derekzyl/smart-incubator/incubator_new_circuit/incubator_new_circuit.kicad_sch

## KiCad design incubator_new_circuit/incubator_new_circuit.kicad_sch (2026-01-31, an earlier design)

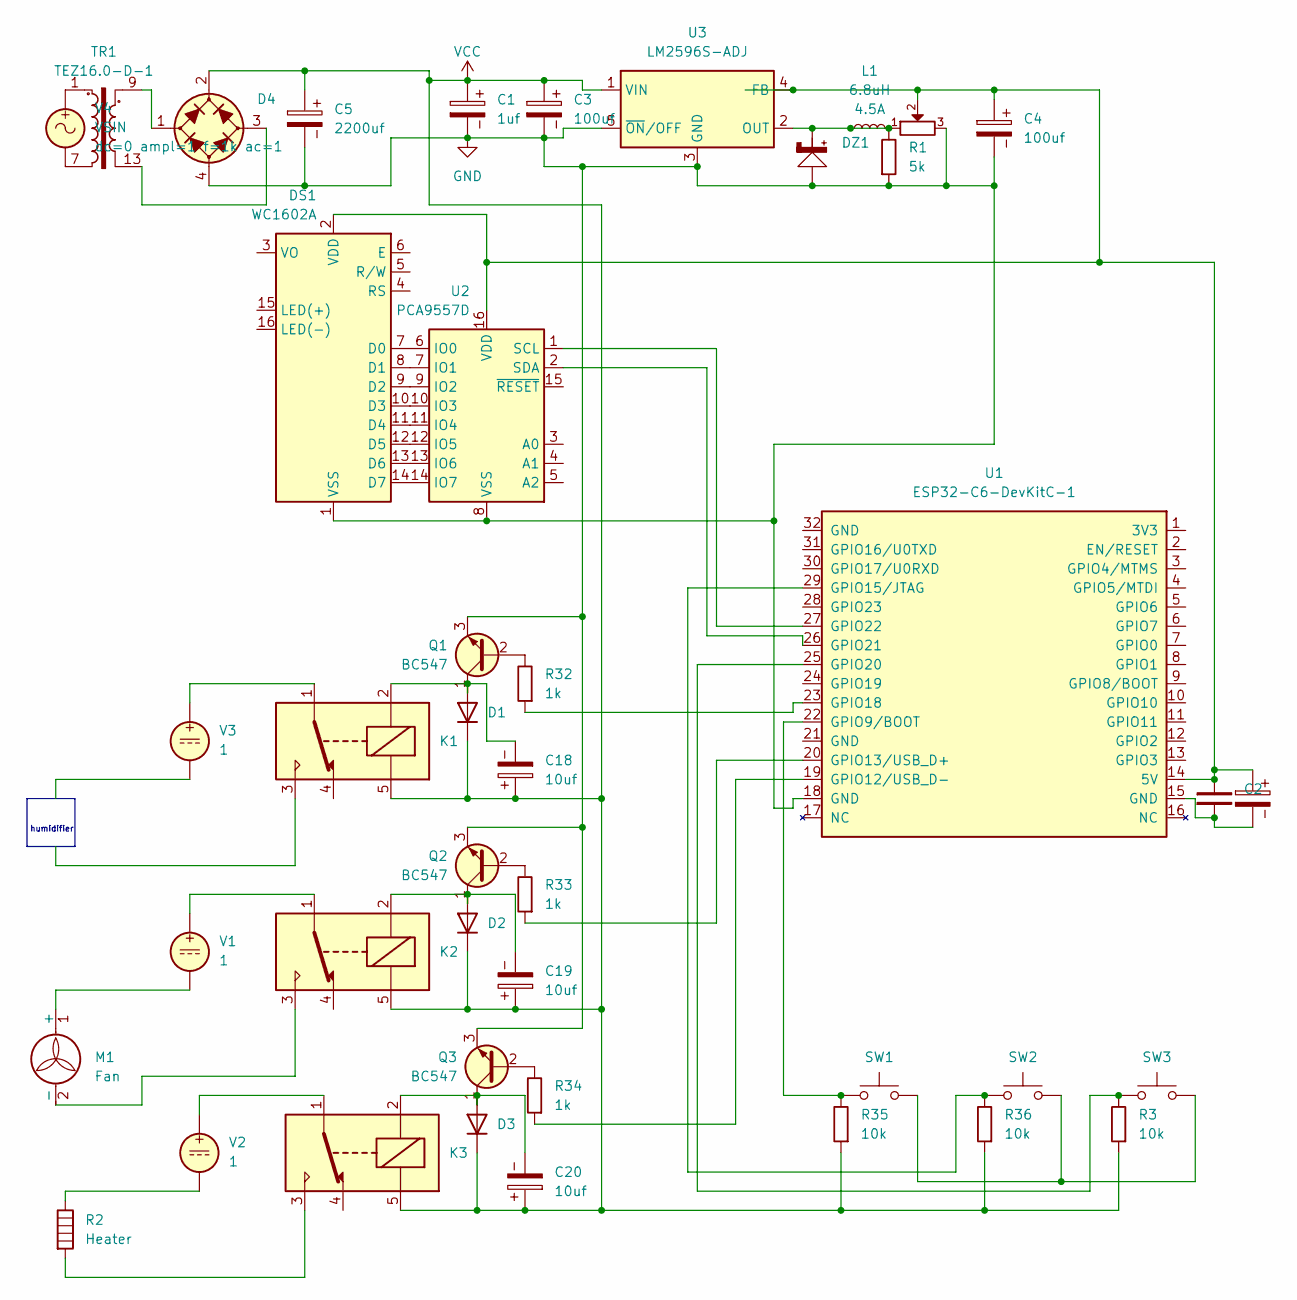
[picture p3: schematic incubator_new_circuit.kicad_sch]

Parts:
C1: 1uf; CP_Radial_D5.0mm_P2.50mm
C2: 104_Ceramic; C_Disc_D5.0mm_W2.5mm_P2.50mm
C3, C4, C17: 100uf; CP_Radial_D5.0mm_P2.50mm
C5: 2200uf; CP_Radial_D5.0mm_P2.50mm
C18, C19, C20: 10uf; CP_Radial_D5.0mm_P2.50mm
D1, D2, D3: 1N4148WT; D_SOD-523
D4: D_Bridge_Generic_AC+AC-
DS1: WC1602A
DZ1: (no value)
K1, K2, K3: SANYOU_SRD_Form_C; Relay_SPDT_SANYOU_SRD_Series_Form_C
L1: 6.8uH; Inductor_7.3x6.6mm
M1: Fan
Q1, Q2, Q3: BC547; TO-92_Inline_Wide_CBE
R1: 5k; R_Axial_DIN0207_L6.3mm_D2.5mm_P10.16mm_Horizontal
R2: Heater
R3, R35, R36: 10k; R_Axial_DIN0207_L6.3mm_D2.5mm_P10.16mm_Horizontal
R32, R33, R34: 1k; R_Axial_DIN0207_L6.3mm_D2.5mm_P10.16mm_Horizontal
RV1: potentiometer_3362P
SW1, SW2, SW3: PTH_12x12mm_h8.0mm; Push_PTH_12x12mm
TR1: TEZ16.0-D-1; Transformer_Breve_TEZ-47x57
U1: ESP32-C6-DevKitC-1
U2: PCA9557D; SO-16_3.9x9.9mm_P1.27mm
U3: LM2596S-ADJ; TO-263-5_TabPin3
V1, V2, V3: 1
V4: VSIN

Connections:
GND: C1.2, C3.2, C4.2, C5.2, D4.4 (-), DS1.1 (VSS), DZ1.2, Q1.3 (E), Q2.3 (E), Q3.3 (E), R1.1, RV1.3, U1.18 (GND), U2.8 (VSS), U3.3 (GND), U3.5 (~ON/OFF)
unnamed: C2.2, C4.1, C17.1, DS1.2 (VDD), RV1.2, U1.14 (5V), U2.16 (VDD), U3.4 (FB)
unnamed: C2.1, C17.2, U1.15 (GND)
unnamed: C18.2, D1.2 (A), K1.2, Q1.1 (C)
unnamed: C19.2, D2.2 (A), K2.2, Q2.1 (C)
unnamed: C20.2, D3.2 (A), K3.2, Q3.1 (C)
unnamed: D4.1, TR1.9
unnamed: D4.3 (2), TR1.13
unnamed: DS1.7 (D0), U2.6 (IO0)
unnamed: DS1.8 (D1), U2.7 (IO1)
unnamed: DS1.9 (D2), U2.9 (IO2)
unnamed: DS1.10 (D3), U2.10 (IO3)
unnamed: DS1.11 (D4), U2.11 (IO4)
unnamed: DS1.12 (D5), U2.12 (IO5)
unnamed: DS1.13 (D6), U2.13 (IO6)
unnamed: DS1.14 (D7), U2.14 (IO7)
unnamed: DZ1.1, L1.1, L1.2, R1.2, RV1.1, U3.2 (OUT)
unnamed: K1.1, V3.1
unnamed: K2.1, V1.1
unnamed: K2.3, M1.2 (-)
unnamed: K3.1, V2.1
unnamed: K3.3, R2.2
unnamed: M1.1 (+), V1.2
unnamed: Q1.2 (B), R32.2
unnamed: Q2.2 (B), R33.2
unnamed: Q3.2 (B), R34.2
unnamed: R2.1, V2.2
unnamed: R3.2, SW3.1, U1.25 (GPIO20)
unnamed: R32.1, U1.23 (GPIO18)
unnamed: R33.1, U1.20 (GPIO13/USB_D+)
unnamed: R34.1, U1.19 (GPIO12/USB_D-)
unnamed: R35.2, SW1.1, U1.22 (GPIO9/BOOT)
unnamed: R36.2, SW2.1, U1.29 (GPIO15/JTAG)
unnamed: SW1.2, SW2.2, SW3.2
unnamed: TR1.1, V4.1
unnamed: TR1.7, V4.2
unnamed: U1.26 (GPIO21), U2.2 (SDA)
unnamed: U1.27 (GPIO22), U2.1 (SCL)
VCC: C1.1, C3.1, C5.1, C18.1, C19.1, C20.1, D1.1 (K), D2.1 (K), D3.1 (K), D4.2 (+), K1.5, K2.5, K3.5, R3.1, R35.1, R36.1, U3.1 (VIN)

Notes on the sheet:
humidifier
