derekzyl/smart-incubator/incubator-firmware/include/servo_control.h

#ifndef SERVO_CONTROL_H
#define SERVO_CONTROL_H

#include <Arduino.h>
#include <ESP32Servo.h>
#include "config.h"

class ServoController {
public:
    ServoController();
    void begin();
    void moveToAngle(int angle);
    int getCurrentAngle();
    
    // Automation helper
    void turnEggs(bool extend, int extendAngle, int retractAngle); // Use settings for angles

private:
    Servo myservo;
    int _currentAngle;
    int _servoPin;
};

#endif // SERVO_CONTROL_H
